Okashii-Kuusou/V-Flow/Images/CEVS-Side_View.jpg

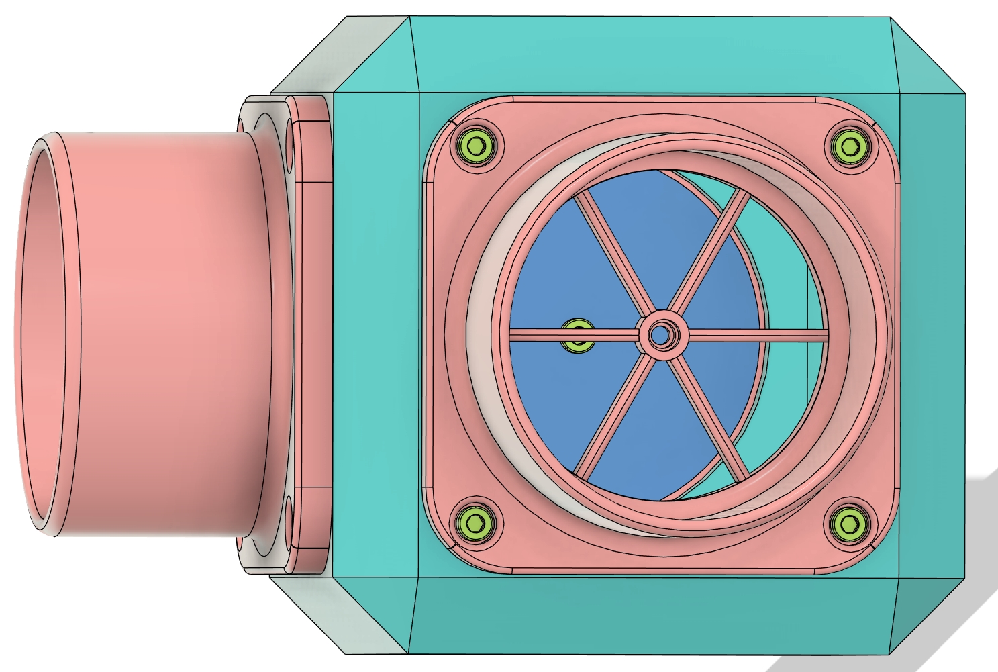
Images/CEVS-Side_View.jpg
