Okashii-Kuusou/V-Flow/Images/Fan_Shroud-Heat_Insert_Example.jpg

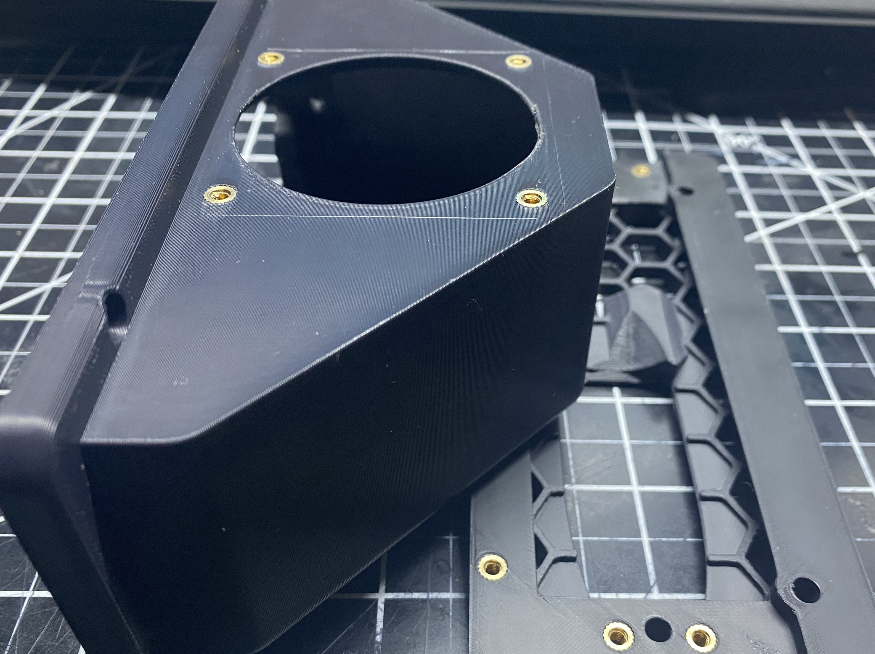
Images/Fan_Shroud-Heat_Insert_Example.jpg
