Okashii-Kuusou/V-Flow/Images/Fan_Shroud_Fastener_View.jpg

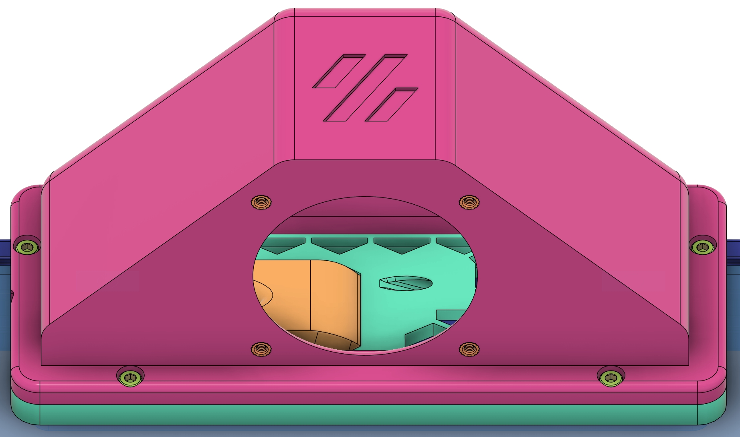
Images/Fan_Shroud_Fastener_View.jpg
