Okashii-Kuusou/V-Flow/Images/V-Flow_Rear-Side_View.jpg

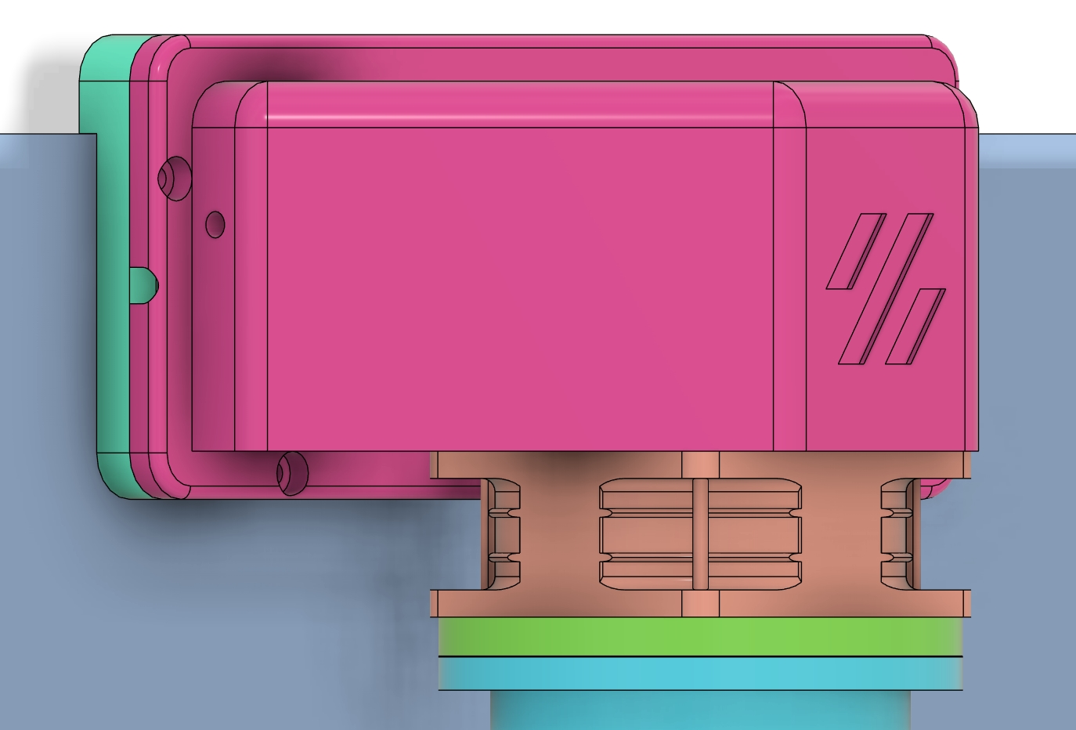
Images/V-Flow_Rear-Side_View.jpg
