Okashii-Kuusou/V-Flow/STL/Printer_Components/Fan_Interface_Ring.stl

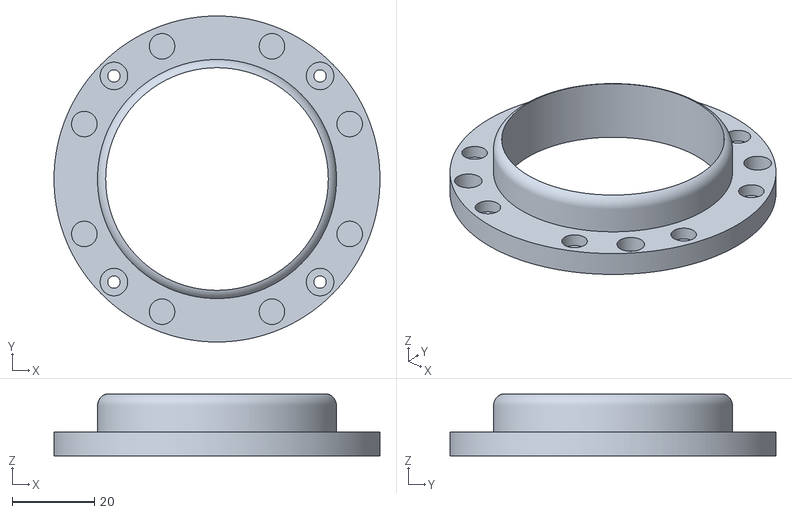
[picture p23: CAD file, 2024-02-04]
STL/Printer_Components/Fan_Interface_Ring.stl
79.1 x 79.1 x 15.0
