Okashii-Kuusou/V-Flow/STL/Printer_Components/Exhaust_Fan_Shroud-8mm_Opening.stl

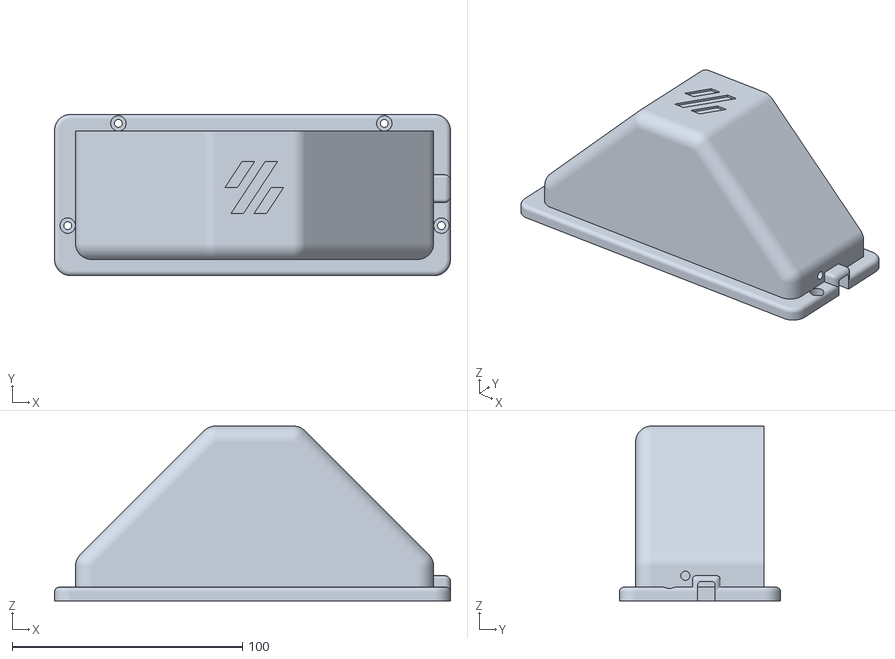
[picture p24: CAD file, 2024-02-04]
STL/Printer_Components/Exhaust_Fan_Shroud-8mm_Opening.stl
172.0 x 70.0 x 76.0
