Okashii-Kuusou/V-Flow/STL/Printer_Components/Front_Mounting_Plate.stl

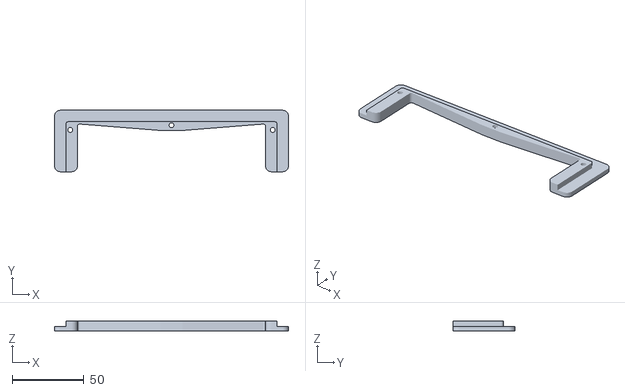
[picture p25: CAD file, 2024-02-04]
STL/Printer_Components/Front_Mounting_Plate.stl
162.8 x 42.8 x 6.75
