Okashii-Kuusou/V-Flow/STL/Printer_Components/Rear_Mounting_Plate.stl

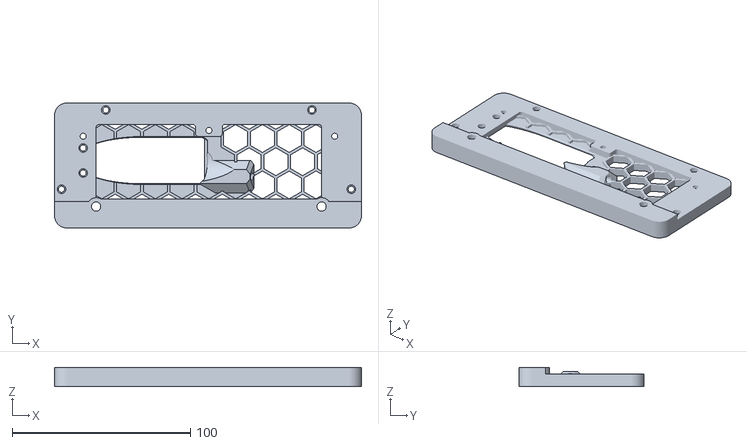
[picture p26: CAD file, 2024-02-04]
STL/Printer_Components/Rear_Mounting_Plate.stl
172.0 x 70.0 x 10.8
